logair/LogAir-Device-DIY/pcb/pdf_plan/logair_pcb_v1.5.png

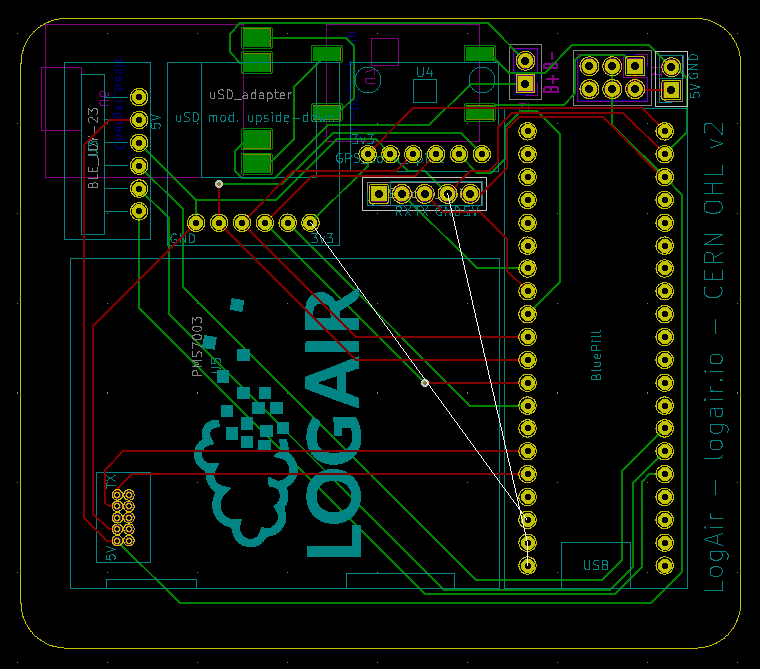
pcb/pdf_plan/logair_pcb_v1.5.png
